uguryildirim24/elicio/tests/test_cad.py

from __future__ import annotations

import importlib.util
import hashlib
import json
import math
import shutil
import subprocess
import sys
import tempfile
import unittest
from pathlib import Path

ROOT = Path(__file__).resolve().parents[1]
SCRIPT = ROOT / "scripts" / "cad" / "bte_fit_shell.py"
MANIFEST_SCRIPT = ROOT / "scripts" / "cad" / "manifest.py"
RENDER_SCRIPT = ROOT / "scripts" / "cad" / "render.py"
MANIFEST = ROOT / "docs" / "fab" / "cad" / "v1" / "manifest.json"
ARTWORK = ("render_medial.png", "render_lateral.png", "drawing.pdf")


def load_cad():
    spec = importlib.util.spec_from_file_location("bte_fit_shell", SCRIPT)
    module = importlib.util.module_from_spec(spec)
    assert spec.loader is not None
    sys.modules["bte_fit_shell"] = module
    spec.loader.exec_module(module)
    return module


CAD = load_cad()

try:
    import matplotlib  # noqa: F401

    HAS_MATPLOTLIB = True
except ImportError:
    HAS_MATPLOTLIB = False
try:
    import trimesh  # noqa: F401

    HAS_TRIMESH = True
except ImportError:
    HAS_TRIMESH = False
HAS_RENDER = HAS_MATPLOTLIB and HAS_TRIMESH
# Review r7: a build needs the whole cad extra, not only build123d: STL checks
# use trimesh and the packing overlays import placement.py (matplotlib). With
# part of the extra missing the build tests skip by name instead of erroring.
HAS_CAD_BUILD = CAD.HAS_BUILD123D and HAS_RENDER
CAD_BUILD_SKIP = "needs the cad extra: build123d, trimesh and matplotlib"
PLACEMENT_SKIP = "needs matplotlib (cad or sheets extra): placement.py draws with it"


def load_manifest_mod():
    spec = importlib.util.spec_from_file_location("cad_manifest", MANIFEST_SCRIPT)
    module = importlib.util.module_from_spec(spec)
    assert spec.loader is not None
    spec.loader.exec_module(module)
    return module


def load_render_mod():
    spec = importlib.util.spec_from_file_location("cad_render", RENDER_SCRIPT)
    module = importlib.util.module_from_spec(spec)
    assert spec.loader is not None
    spec.loader.exec_module(module)
    return module


class CadMathTests(unittest.TestCase):
    def test_default_chord_and_radius_match_plan(self) -> None:
        path = CAD.make_path(48.4, 3.0)
        self.assertAlmostEqual(path.chord, 47.9005234, places=6)
        self.assertAlmostEqual(path.radius, 97.1025059, places=6)

    def test_origin_and_mid_arc_and_tail(self) -> None:
        path = CAD.make_path(48.4, 3.0)
        self.assertEqual(CAD.p_xyz(path, 0.0, 0.0, 0.0), (0.0, 0.0, 0.0))
        mid = CAD.p_xyz(path, 0.0, 24.2, 0.0)
        self.assertAlmostEqual(mid[0], 3.0, places=6)
        tail = CAD.p_xyz(path, 0.0, 48.4, 0.0)
        self.assertAlmostEqual(tail[0], 0.0, places=6)
        self.assertAlmostEqual(tail[2], -path.chord, places=6)

    def test_chord_gate_at_bow_1_and_3(self) -> None:
        gate3 = CAD.make_path(48.4, 3.0).chord + 3.0
        gate1 = CAD.make_path(48.4, 1.0).chord + 3.0
        self.assertAlmostEqual(gate3, 50.9005234, places=6)
        self.assertAlmostEqual(gate1, 51.3448596, places=6)

    def test_wire_channel_openings_match_finding_23(self) -> None:
        expected = {
            1.0: (39.4444, 1.0891),
            3.0: (39.6437, 0.9383),
            8.0: (40.0750, 0.5373),
        }
        for bow, (s_entry, physical) in expected.items():
            with self.subTest(bow=bow):
                report = CAD.wire_channel_opening(CAD.make_path(48.4, bow).radius)
                self.assertAlmostEqual(report["s_entry"], s_entry, places=3)
                self.assertAlmostEqual(report["physical_opening"], physical, places=3)
                self.assertGreater(report["physical_opening"], 0.0)

    def test_crease_bow_clamp(self) -> None:
        self.assertEqual(CAD.clamp_crease_bow(0.2), 1.0)
        self.assertEqual(CAD.clamp_crease_bow(11.0), 8.0)
        self.assertEqual(CAD.clamp_crease_bow(3.0), 3.0)


class CadCheckTests(unittest.TestCase):
    def test_m1_below_gate_fails_with_parameter_and_number(self) -> None:
        with self.assertRaises(CAD.CheckFail) as ctx:
            CAD.cli(["--set", "M1=40", "--checks-only"])
        message = str(ctx.exception)
        self.assertIn("M1", message)
        self.assertIn("40", message)
        self.assertIn("gate", message)

    def test_variant_outside_matrix_fails_before_export(self) -> None:
        with self.assertRaises(CAD.CheckFail) as ctx:
            CAD.cli(["--set", "VARIANT=medium", "--checks-only"])
        message = str(ctx.exception)
        self.assertIn("VARIANT", message)
        self.assertIn("medium", message)

    def test_preload_outside_matrix_fails_before_export(self) -> None:
        with self.assertRaises(CAD.CheckFail) as ctx:
            CAD.cli(["--set", "HOOK_PRELOAD=3", "--checks-only"])
        message = str(ctx.exception)
        self.assertIn("HOOK_PRELOAD", message)
        self.assertIn("3", message)

    def test_reference_checks_pass(self) -> None:
        self.assertEqual(CAD.cli(["--checks-only"]), 0)

    def test_plan_named_checks_are_present(self) -> None:
        params, _used = CAD.build_reference_params(variant="full", preload=1.5)
        names = {check.name for check in CAD.run_pre_cad_checks(params)}
        for expected in (
            "matrix",
            "M1_gate",
            "HOOK_RADIUS",
            "CONTACT_STACK",
            "keep-out: CONTACT_1 to superior low-u pad",
            "fit: tongue 0.5 : slot 0.9, y",
            "wall: top end wall at LIP_GROOVE",
            "E1",
            "E5_bump",
            "WIRE_CHANNEL_opening",
        ):
            self.assertIn(expected, names)

    def test_pad_keepout_gap_is_positive_at_supported_bows(self) -> None:
        for bow in (1.0, 3.0, 8.0):
            with self.subTest(bow=bow):
                params, _used = CAD.build_reference_params(
                    variant="full", preload=1.5, overrides={"CREASE_BOW": bow}
                )
                path = CAD.make_path(48.4, bow)
                gaps = CAD.keepout_clearances(params, path)
                self.assertGreater(gaps["CONTACT_1 to superior low-u pad"], 0.09)

    def test_fit_drift_fails(self) -> None:
        params, _used = CAD.build_reference_params(variant="full", preload=1.5)
        original = CAD.LIP_S
        CAD.LIP_S = (-1.2, -0.1)
        try:
            with self.assertRaises(CAD.CheckFail) as ctx:
                CAD.run_pre_cad_checks(params)
        finally:
            CAD.LIP_S = original
        self.assertIn("E5_lip", str(ctx.exception))


class CadOverlayTests(unittest.TestCase):
    def _params(self, argv: list[str]) -> dict:
        args = CAD.parse_args(argv)
        overrides, from_m = CAD.resolve_overrides(args)
        params, _used = CAD.build_reference_params(
            variant="full", preload=1.5, overrides=overrides, crease_bow_from_m=from_m
        )
        return params

    def _overlay(self, text: str) -> Path:
        handle = tempfile.NamedTemporaryFile("w", suffix=".toml", delete=False)
        handle.write(text)
        handle.close()
        self.addCleanup(Path(handle.name).unlink)
        return Path(handle.name)

    def test_default_toml_as_params_is_not_an_overlay(self) -> None:
        args = CAD.parse_args(["--params", str(CAD.DEFAULT_PARAMS_PATH)])
        overrides, from_m = CAD.resolve_overrides(args)
        self.assertEqual(overrides, {})
        self.assertFalse(from_m)

    def test_empty_overlay_keeps_default_bow(self) -> None:
        params = self._params(["--params", str(self._overlay("# nothing measured\n"))])
        self.assertEqual(params["CREASE_BOW"], 3.0)

    def test_overlay_with_m1_only_keeps_default_bow(self) -> None:
        params = self._params(["--params", str(self._overlay("M1 = 53.0\n"))])
        self.assertEqual(params["CREASE_BOW"], 3.0)

    def test_overlay_with_m1_and_m2_computes_and_clamps_bow(self) -> None:
        params = self._params(["--params", str(self._overlay("M1 = 52.0\nM2 = 58.0\n"))])
        self.assertAlmostEqual(params["CREASE_BOW_COMPUTED"], 11.0014, places=3)
        self.assertEqual(params["CREASE_BOW"], 8.0)

    def test_overlay_crease_bow_wins_over_m1_m2(self) -> None:
        text = "M1 = 52.0\nM2 = 58.0\nCREASE_BOW = 2.0\n"
        params = self._params(["--params", str(self._overlay(text))])
        self.assertEqual(params["CREASE_BOW"], 2.0)

    def test_m8_drives_hook_radius(self) -> None:
        params = self._params(["--set", "M8=13"])
        self.assertAlmostEqual(params["HOOK_RADIUS"], 13.0 + 1.75 + 0.75)
        self.assertEqual(CAD.cli(["--set", "M8=13", "--checks-only"]), 0)

    def test_unknown_key_fails(self) -> None:
        with self.assertRaises(CAD.CheckFail) as ctx:
            CAD.cli(["--set", "M9=12", "--checks-only"])
        self.assertIn("M9", str(ctx.exception))

    def test_fixed_geometry_key_fails(self) -> None:
        with self.assertRaises(CAD.CheckFail) as ctx:
            CAD.cli(["--set", "BODY_WIDTH=15", "--checks-only"])
        self.assertIn("BODY_WIDTH=15", str(ctx.exception))

    @unittest.skipUnless(HAS_MATPLOTLIB, PLACEMENT_SKIP)
    def test_stage_b_mock_false_checks_run(self) -> None:
        self.assertEqual(
            CAD.cli(["--set", "MOCK_CONTACTS=false", "--set", "CABLE_EXIT_S=35", "--checks-only"]), 0
        )
        params, _used = CAD.build_reference_params(
            variant="full", preload=1.5, overrides={"MOCK_CONTACTS": False, "CABLE_EXIT_S": 35.0}
        )
        names = {check.name: check for check in CAD.run_pre_cad_checks(params)}
        self.assertFalse(names["Q21_REF_lug pre-CAD"].passed)
        self.assertNotIn("E1", names)
        self.assertNotIn("E5_bump", names)
        for name in (
            "PLACEMENT_contacts",
            "BOARD_underside_clear pre-CAD",
            "CELL_envelope pre-CAD",
            "CABLE_EXIT_cavity pre-CAD",
            "TAB_envelope_air pre-CAD",
            "M1_gate",
        ):
            self.assertTrue(names[name].passed, name)


@unittest.skipUnless(HAS_CAD_BUILD, CAD_BUILD_SKIP)
class CadRegenTests(unittest.TestCase):
    def test_reference_regen_matches_committed_hashes(self) -> None:
        manifest = json.loads(MANIFEST.read_text(encoding="utf-8"))
        expected = {
            f"{part}.{ext}" for part in CAD.ORDER_PARTS for ext in ("step", "stl", "3mf")
        }
        self.assertEqual(set(manifest["files"]), expected)
        self.assertEqual(manifest["parts"], list(CAD.ORDER_PARTS))
        self.assertEqual(sum(manifest["quantities"].values()), 6)
        committed = {p.name for p in MANIFEST.parent.iterdir()}
        # placement*.svg are WP6 drawings, regenerated by tests/test_placement.py.
        placement = {
            "placement.svg",
            "placement_A.svg",
            "placement_B.svg",
            "placement_C.svg",
            "placement_E.svg",
        }
        v2_drawings = {p.name for p in MANIFEST.parent.glob("placement_v2_*.svg")}
        self.assertGreaterEqual(len(v2_drawings), 1)
        self.assertEqual(committed, expected | {"manifest.json"} | placement | set(ARTWORK) | v2_drawings)
        for name, meta in manifest["files"].items():
            with self.subTest(committed=name):
                self.assertEqual(
                    CAD.sha256_file(MANIFEST.parent / name), meta["sha256"], name
                )
        with tempfile.TemporaryDirectory() as temp_dir:
            CAD.build_and_export(Path(temp_dir))
            written = {p.name for p in Path(temp_dir).iterdir()}
            self.assertEqual(written, expected | {"manifest.json"})
            regenerated = json.loads((Path(temp_dir) / "manifest.json").read_text("utf-8"))
            for name in sorted(expected):
                with self.subTest(regenerated=name):
                    path = Path(temp_dir) / name
                    self.assertEqual(CAD.sha256_file(path), manifest["files"][name]["sha256"])
                    self.assertEqual(
                        regenerated["files"][name]["sha256"], manifest["files"][name]["sha256"]
                    )
            self.assertTrue(all(check["passed"] for check in regenerated["checks"]))
            self.assertEqual(regenerated["commit"], manifest["commit"])
            self.assertNotIn("views", regenerated)
            # Everything else the writer records must match the committed file,
            # so a generator change (a new note, a changed check) cannot leave
            # a stale manifest behind.
            committed_rest = {
                k: v for k, v in manifest.items() if not k.startswith("views")
            }
            self.assertEqual(regenerated, committed_rest)


class ManifestSchemaTests(unittest.TestCase):
    def test_committed_manifest_validates(self) -> None:
        mod = load_manifest_mod()
        payload = mod.load_manifest(MANIFEST)
        mod.validate(payload)
        mod.validate_bytes(payload, MANIFEST.parent)

    def test_validator_rejects_missing_key(self) -> None:
        mod = load_manifest_mod()
        payload = json.loads(MANIFEST.read_text(encoding="utf-8"))
        del payload["files"]
        with self.assertRaises(mod.ManifestError) as ctx:
            mod.validate(payload)
        self.assertIn("files", str(ctx.exception))
        self.assertIn("missing key", str(ctx.exception))


@unittest.skipUnless(HAS_RENDER, "needs the cad extra: matplotlib/trimesh is not installed")
class CadRenderTests(unittest.TestCase):
    def test_renders_and_drawing_regen_byte_identical(self) -> None:
        render = load_render_mod()
        v1 = MANIFEST.parent
        with tempfile.TemporaryDirectory() as temp_dir:
            dest = Path(temp_dir)
            for name in ("body_full_p15.stl", "body_thin_p15.stl", "lid.stl", "manifest.json"):
                shutil.copy2(v1 / name, dest / name)
            self.assertEqual(render.main(["--out", str(dest)]), 0)
            for name in ARTWORK:
                with self.subTest(name=name):
                    self.assertEqual(
                        CAD.sha256_file(dest / name),
                        CAD.sha256_file(v1 / name),
                        name,
                    )
            again = Path(tempfile.mkdtemp())
            self.addCleanup(shutil.rmtree, again, True)
            for name in ("body_full_p15.stl", "body_thin_p15.stl", "lid.stl", "manifest.json"):
                shutil.copy2(v1 / name, again / name)
            self.assertEqual(render.main(["--out", str(again)]), 0)
            committed_views = json.loads(MANIFEST.read_text(encoding="utf-8"))["views"]
            rendered_views = json.loads((again / "manifest.json").read_text("utf-8"))["views"]
            self.assertEqual(rendered_views, committed_views)
            for name in ARTWORK:
                with self.subTest(second=name):
                    self.assertEqual(
                        CAD.sha256_file(dest / name),
                        CAD.sha256_file(again / name),
                        name,
                    )


@unittest.skipUnless(HAS_CAD_BUILD, CAD_BUILD_SKIP)
class CadBuildGuardTests(unittest.TestCase):
    def test_clamp_limits_build_one_solid(self) -> None:
        for bow in (1.0, 8.0):
            with self.subTest(bow=bow), tempfile.TemporaryDirectory() as temp_dir:
                result = CAD.build_and_export(
                    Path(temp_dir), overrides={"CREASE_BOW": bow}, parts=("body_full_p15",)
                )
                self.assertEqual(len(result["files"]), 3)

    def test_subset_build_refuses_to_leave_stale_parts(self) -> None:
        with tempfile.TemporaryDirectory() as temp_dir:
            (Path(temp_dir) / "manifest.json").write_text(
                json.dumps({"files": {"body_thin_p15.stl": {}}}), encoding="utf-8"
            )
            with self.assertRaises(CAD.CheckFail) as ctx:
                CAD.build_and_export(Path(temp_dir), parts=("coupon",))
            self.assertIn("body_thin_p15", str(ctx.exception))

    def test_m1_below_gate_does_not_write_files(self) -> None:
        with tempfile.TemporaryDirectory() as temp_dir:
            with self.assertRaises(CAD.CheckFail):
                CAD.cli(
                    [
                        "--set",
                        "M1=40",
                        "--out",
                        temp_dir,
                    ]
                )
            self.assertEqual(list(Path(temp_dir).iterdir()), [])


STAGE_B_FILE = ROOT / "scripts" / "cad" / "params" / "stageb_provisional.toml"
# The provisional reading: plan §3.3 CABLE_EXIT s 36 cuts a corner pad (review r4 decision 24).
STAGE_B_BASE = {"MOCK_CONTACTS": False, "CABLE_EXIT_S": 35.0}


def stage_b_params(overrides: dict | None = None, variant: str = "full") -> dict:
    merged = dict(STAGE_B_BASE)
    merged.update(overrides or {})
    params, _used = CAD.build_reference_params(variant=variant, preload=1.5, overrides=merged)
    return params


@unittest.skipUnless(HAS_MATPLOTLIB, PLACEMENT_SKIP)
class CadStageBTests(unittest.TestCase):
    def test_packing_a_is_plan_shell(self) -> None:
        params = stage_b_params({"PACKING": "A"})
        self.assertEqual(params["PACKING"], "A")
        self.assertAlmostEqual(params["BODY_WIDTH"], 17.0)
        self.assertAlmostEqual(params["BODY_ARC"], 48.4)

    def test_packing_c_widens_body_and_uses_placement_pads(self) -> None:
        params = stage_b_params({"PACKING": "C"})
        self.assertEqual(params["PACKING"], "C")
        self.assertAlmostEqual(params["BODY_WIDTH"], 20.0)
        self.assertEqual(params["CAVITY_U"], [1.5, 18.5])
        self.assertEqual(params["LEAD_PADS"]["SIG1"], [7.5, 29.35])
        self.assertEqual(params["LEAD_PADS"]["SIG2"], [13.5, 21.35])
        self.assertEqual(params["LEAD_PADS"]["REF"], [5.5, 29.35])
        placement = CAD.load_placement()
        self.assertEqual(
            params["LEAD_PADS"]["SIG1"],
            list(placement.PADS_BY_OPTION["C"]["SIG1"]),
        )

    def test_packing_b_lengthens_arc_and_moves_tail(self) -> None:
        params = stage_b_params({"PACKING": "B"})
        self.assertAlmostEqual(params["BODY_ARC"], 51.9)
        self.assertAlmostEqual(params["TAIL_DS"], 3.5)
        self.assertAlmostEqual(params["TAIL_S0"], 41.7)
        self.assertAlmostEqual(params["CONTACT_REF_S"], 46.5)
        self.assertEqual(params["WIRE_S"], [41.7, 44.0])

    def test_pads_are_not_copied_into_the_cad_script(self) -> None:
        text = SCRIPT.read_text(encoding="utf-8")
        self.assertNotIn("29.35", text)
        self.assertNotIn("21.35", text)

    def test_q21_pre_cad_records_failure_with_numbers(self) -> None:
        params = stage_b_params()
        q21 = {c.name: c for c in CAD.run_pre_cad_checks(params)}["Q21_REF_lug pre-CAD"]
        self.assertFalse(q21.passed)
        self.assertEqual(q21.numbers["lug_top_y"], 8.23)
        self.assertEqual(q21.numbers["lid_y"], 8.0)
        self.assertEqual(q21.numbers["barrel_outer"], 4.54)
        self.assertEqual(q21.numbers["pocket_r"], 3.75)

    def test_keepout_on_rib_fails_with_gap(self) -> None:
        with self.assertRaises(CAD.CheckFail) as ctx:
            CAD.cli(
                ["--set", "MOCK_CONTACTS=false", "--set", "CONTACT_1_S=17.9", "--checks-only"]
            )
        message = str(ctx.exception)
        self.assertIn("keep-out", message)
        self.assertIn("gap", message)

    def test_tab_height_3_fails_board_clearance(self) -> None:
        with self.assertRaises(CAD.CheckFail) as ctx:
            CAD.cli(["--set", "MOCK_CONTACTS=false", "--set", "TAB_HEIGHT=3", "--checks-only"])
        message = str(ctx.exception)
        self.assertIn("BOARD_underside_clear", message)
        self.assertIn("envelope_top=4.5", message)

    def test_cable_exit_in_battery_fails(self) -> None:
        with self.assertRaises(CAD.CheckFail) as ctx:
            CAD.cli(
                ["--set", "MOCK_CONTACTS=false", "--set", "CABLE_EXIT_S=10", "--checks-only"]
            )
        message = str(ctx.exception)
        self.assertIn("CABLE_EXIT_cavity", message)
        self.assertIn("CABLE_EXIT_S=10", message)
        self.assertIn("board_side_of_rib=0.0", message)

    def test_cable_exit_at_plan_s36_meets_a_corner_pad_pre_cad(self) -> None:
        with self.assertRaises(CAD.CheckFail) as ctx:
            CAD.cli(["--set", "MOCK_CONTACTS=false", "--checks-only"])
        self.assertIn("CABLE_EXIT_cavity pre-CAD", str(ctx.exception))
        self.assertIn("corner_pad_s_gap=-0.6", str(ctx.exception))

    def test_cell_too_wide_fails(self) -> None:
        params = stage_b_params()
        original = CAD.BATTERY_U
        CAD.BATTERY_U = (3.1, 8.0)
        try:
            with self.assertRaises(CAD.CheckFail) as ctx:
                CAD.run_pre_cad_checks(params)
        finally:
            CAD.BATTERY_U = original
        self.assertIn("CELL_envelope", str(ctx.exception))
        self.assertIn("clear_u=-5.5", str(ctx.exception))

    def test_cell_does_not_fit_a_thin_body_pre_cad(self) -> None:
        with self.assertRaises(CAD.CheckFail) as ctx:
            CAD.run_pre_cad_checks(stage_b_params(variant="thin"))
        self.assertIn("CELL_envelope pre-CAD", str(ctx.exception))
        self.assertIn("clear_y=-1.2", str(ctx.exception))

    def test_closure_passed_restores_e1_e3_e5(self) -> None:
        names = {c.name for c in CAD.run_pre_cad_checks(stage_b_params({"CLOSURE_PASSED": True}))}
        self.assertIn("E1", names)
        self.assertIn("E3", names)
        self.assertIn("E5_bump", names)
        names = {c.name for c in CAD.run_pre_cad_checks(stage_b_params())}
        self.assertNotIn("E1", names)

    def test_provisional_file_defaults(self) -> None:
        args = CAD.parse_args(["--params", str(STAGE_B_FILE)])
        overrides, _from_m = CAD.resolve_overrides(args)
        self.assertFalse(overrides["MOCK_CONTACTS"])
        self.assertEqual(overrides["PACKING"], "C")
        self.assertFalse(overrides["CLOSURE_PASSED"])
        self.assertEqual(overrides["TAB_HEIGHT"], 2.0)
        self.assertEqual(overrides["CABLE_EXIT_S"], 35.0)
        header = STAGE_B_FILE.read_text(encoding="utf-8")
        for question in ("Q20", "Q22", "Q21", "Q18", "Q11", "Q17", "WP7a", "decision 24", "decision 25"):
            self.assertIn(question, header)

    def test_order1_overlay_refuses_stage_b_keys(self) -> None:
        for item in ("CONTACT_1_U=7.0", "PACKING=B", "CLOSURE_PASSED=true", "CABLE_EXIT_S=35"):
            with self.subTest(item=item):
                with self.assertRaises(CAD.CheckFail) as ctx:
                    CAD.cli(["--set", item, "--checks-only"])
                self.assertIn("MOCK_CONTACTS = false", str(ctx.exception))
                self.assertIn(item.split("=")[0], str(ctx.exception))

    def test_stage_b_contacts_off_the_placement_sites_fail(self) -> None:
        with self.assertRaises(CAD.CheckFail) as ctx:
            CAD.run_pre_cad_checks(stage_b_params({"CONTACT_1_S": 22.5}))
        message = str(ctx.exception)
        self.assertIn("PLACEMENT_contacts", message)
        self.assertIn("drift=0.5", message)

    def test_stage_b_refuses_v1_out(self) -> None:
        params = stage_b_params()
        with self.assertRaises(CAD.CheckFail) as ctx:
            CAD.assert_stage_b_out_dir(CAD.V1_DIR, params)
        self.assertIn("v1", str(ctx.exception).lower())
        with self.assertRaises(CAD.CheckFail):
            CAD.assert_stage_b_out_dir(CAD.V2_DIR, params)

    def test_stage_b_manifest_validator(self) -> None:
        mod = load_manifest_mod()
        payload = json.loads(MANIFEST.read_text(encoding="utf-8"))
        mod.validate(payload)
        row = {"passed": True, "detail": "d", "numbers": {}, "bodies": {"body_full_p15": {"passed": True}}}
        payload.update(
            stage="B",
            provisional=True,
            packing="C",
            closure_passed=False,
            contact_source="plan §3.3 defaults",
            stage_b={name: dict(row) for name in mod.STAGE_B_CHECKS},
            stage_b_failing=[],
            stage_b_passed=True,
        )
        mod.validate(payload)
        payload["stage_b"]["Q21_REF_lug"] = {**row, "passed": False, "bodies": {"body_full_p15": {"passed": False}}}
        with self.assertRaises(mod.ManifestError):
            mod.validate(payload)
        payload["stage_b_failing"] = ["Q21_REF_lug"]
        with self.assertRaises(mod.ManifestError):
            mod.validate(payload)
        payload["stage_b_passed"] = False
        mod.validate(payload)
        del payload["stage_b"]["CELL_envelope"]
        with self.assertRaises(mod.ManifestError):
            mod.validate(payload)


@unittest.skipUnless(HAS_CAD_BUILD, CAD_BUILD_SKIP)
class CadStageBBuildTests(unittest.TestCase):
    """Stage B checks measured on solids: one passing body, then each check's
    failing case with the parameter that breaks it and the number it reports."""

    @classmethod
    def setUpClass(cls) -> None:
        cls.params = stage_b_params()
        cls.body, cls.lid, cls.path, cls.notes = CAD.build_body_and_lid(cls.params)

    def rows(self, params=None, body=None, lid=None, notes=None) -> dict:
        checks = CAD.run_stage_b_solid_checks(
            body or self.body,
            lid or self.lid,
            self.path,
            params or self.params,
            (notes or self.notes)["stage_b_cuts"],
            raise_on_fail=False,
        )
        return {c.name: c for c in checks}

    def test_provisional_c_passes_every_check_but_q21(self) -> None:
        rows = self.rows()
        self.assertEqual(set(rows), set(CAD.STAGE_B_CHECK_NAMES))
        self.assertEqual([n for n, c in rows.items() if not c.passed], ["Q21_REF_lug"])
        q21 = rows["Q21_REF_lug"].numbers
        self.assertEqual(q21["lug_top_y"], 8.23)
        self.assertEqual(q21["lid_y"], 8.0)
        self.assertEqual(q21["barrel_outer"], 4.54)
        self.assertEqual(q21["pocket_r"], 3.75)
        self.assertEqual(rows["CONTACT_HOLE_wall"].numbers["removed_SIG1_mm3"], 9.9078)
        self.assertEqual(rows["BOARD_underside_clear"].numbers["board_underside"], 4.3)
        self.assertEqual(rows["CELL_envelope"].numbers["clear_y_lid"], 0.4)
        # Q21 is recorded, not raised.
        CAD.run_stage_b_solid_checks(self.body, self.lid, self.path, self.params, self.notes["stage_b_cuts"])

    def test_stage_b_lid_is_not_embossed_as_the_order1_gauge(self) -> None:
        self.assertEqual(self.notes["emboss"], "ELICIO V2 R FULL P15 REF")
        self.assertEqual(self.notes["emboss_h"], 0.4)
        self.assertEqual(self.notes["emboss_s"], 10.0)

    def test_keepout_signal_fails_when_nylon_is_inside(self) -> None:
        params = dict(self.params, CONTACT_1_S=19.0)
        row = self.rows(params)["KEEPOUT_SIGNAL_air"]
        self.assertFalse(row.passed)
        self.assertGreater(row.numbers["SIG1_body_mm3"], 1.0)
        with self.assertRaises(CAD.CheckFail) as ctx:
            CAD.run_stage_b_solid_checks(self.body, self.lid, self.path, params, self.notes["stage_b_cuts"])
        self.assertIn("KEEPOUT_SIGNAL_air", str(ctx.exception))

    def test_tab_envelope_fails_into_the_side_wall(self) -> None:
        params = dict(self.params, TAB_DEG={"SIG1": 110.0, "SIG2": 0.0})
        row = self.rows(params)["TAB_envelope_air"]
        self.assertFalse(row.passed)
        self.assertGreater(row.numbers["SIG2_body_mm3"], 0.5)
        self.assertEqual(row.numbers["SIG1_body_mm3"], 0.0)

    def test_board_underside_fails_with_a_3_mm_tab(self) -> None:
        row = self.rows(dict(self.params, TAB_HEIGHT=3.0))["BOARD_underside_clear"]
        self.assertFalse(row.passed)
        self.assertEqual(row.numbers["envelope_top"], 4.5)
        self.assertEqual(row.numbers["board_underside"], 4.3)

    def test_ref_wire_fails_when_it_runs_in_the_floor(self) -> None:
        original = CAD.WIRE_Y
        CAD.WIRE_Y = (0.4, 2.0)
        try:
            row = self.rows()["REF_WIRE_envelope"]
        finally:
            CAD.WIRE_Y = original
        self.assertFalse(row.passed)
        self.assertGreater(row.numbers["body_mm3"], 1.0)

    def test_closure_flag_must_match_the_solids(self) -> None:
        row = self.rows(dict(self.params, CLOSURE_PASSED=True))["CLOSURE_PASSED"]
        self.assertFalse(row.passed)
        self.assertEqual(row.numbers["flag"], 1.0)
        self.assertEqual(row.numbers["tongue"], 0.0)

    def test_hole_in_side_wall_fails_wall_only_check(self) -> None:
        params = stage_b_params({"CONTACT_1_U": 0.5})
        body, lid, path, notes = CAD.build_body_and_lid(params)
        with self.assertRaises(CAD.CheckFail) as ctx:
            CAD.run_stage_b_solid_checks(body, lid, path, params, notes["stage_b_cuts"])
        self.assertIn("CONTACT_HOLE_wall", str(ctx.exception))
        removed = notes["stage_b_cuts"]["hole_removed_mm3"]["SIG1"]
        self.assertLess(removed, 0.98 * 9.9078)

    def test_cable_exit_at_plan_s36_cuts_a_corner_pad(self) -> None:
        params = stage_b_params({"CABLE_EXIT_S": 36.0})
        body, lid, path, notes = CAD.build_body_and_lid(params)
        row = self.rows(params, body, lid, notes)["CABLE_EXIT_cavity"]
        self.assertFalse(row.passed)
        self.assertAlmostEqual(row.numbers["nylon_in_cavity_mm3"], 0.99, delta=0.01)

    def test_cell_envelope_fails_on_a_thin_body(self) -> None:
        params = stage_b_params(variant="thin")
        body, lid, path, notes = CAD.build_body_and_lid(params)
        rows = {
            c.name: c
            for c in CAD.run_stage_b_solid_checks(
                body, lid, path, params, notes["stage_b_cuts"], raise_on_fail=False
            )
        }
        row = rows["CELL_envelope"]
        self.assertFalse(row.passed)
        self.assertGreater(row.numbers["lid_mm3"], 150.0)
        self.assertEqual(rows["Q21_REF_lug"].numbers["lid_y"], 6.0)

    def test_closure_passed_puts_the_e1_web_in_the_ref_pocket(self) -> None:
        params = stage_b_params({"CLOSURE_PASSED": True})
        body, lid, path, notes = CAD.build_body_and_lid(params)
        rows = {
            c.name: c
            for c in CAD.run_stage_b_solid_checks(
                body, lid, path, params, notes["stage_b_cuts"], raise_on_fail=False
            )
        }
        self.assertTrue(rows["CLOSURE_PASSED"].passed)
        ref = rows["KEEPOUT_REF_air"]
        self.assertFalse(ref.passed)
        self.assertAlmostEqual(ref.numbers["pocket_lid_mm3"], 2.48, delta=0.02)

    def test_guard_refuses_a_build_without_every_stage_b_check(self) -> None:
        original = CAD.run_stage_b_solid_checks

        def partial(*args, **kwargs):
            return [c for c in original(*args, **kwargs) if c.name != "CELL_envelope"]

        CAD.run_stage_b_solid_checks = partial
        try:
            with tempfile.TemporaryDirectory() as temp_dir:
                with self.assertRaises(CAD.CheckFail) as ctx:
                    CAD.build_and_export(
                        Path(temp_dir), overrides=dict(STAGE_B_BASE), parts=("body_full_p15",)
                    )
                self.assertEqual(list(Path(temp_dir).iterdir()), [])
        finally:
            CAD.run_stage_b_solid_checks = original
        self.assertIn("Stage B checks missing", str(ctx.exception))
        self.assertIn("CELL_envelope", str(ctx.exception))

    def test_stage_b_build_needs_a_body(self) -> None:
        with tempfile.TemporaryDirectory() as temp_dir:
            with self.assertRaises(CAD.CheckFail) as ctx:
                CAD.build_and_export(Path(temp_dir), overrides=dict(STAGE_B_BASE), parts=("lid",))
        self.assertIn("needs a body", str(ctx.exception))

    def test_provisional_build_from_the_readme_command(self) -> None:
        cmd = [sys.executable, str(SCRIPT), "--params", str(STAGE_B_FILE)]
        payloads = []
        for _ in range(2):
            with tempfile.TemporaryDirectory() as temp_dir:
                dest = Path(temp_dir)
                done = subprocess.run(cmd + ["--out", str(dest)], capture_output=True, text=True)
                self.assertEqual(done.returncode, CAD.STAGE_B_NOT_PASSED_EXIT, done.stderr)
                self.assertIn("STAGE B NOT PASSED", done.stderr)
                self.assertIn("Q21_REF_lug", done.stderr)
                payload = json.loads((dest / "manifest.json").read_text(encoding="utf-8"))
                self.assertEqual(
                    sorted(p.name for p in dest.iterdir()),
                    sorted(
                        [f"{part}.{ext}" for part in CAD.STAGE_B_PARTS for ext in ("3mf", "step", "stl")]
                        + ["manifest.json"]
                    ),
                )
                payloads.append(payload)
        payload, again = payloads
        self.assertEqual(again["files"], payload["files"])
        self.assertEqual(payload["stage"], "B")
        self.assertTrue(payload["provisional"])
        self.assertEqual(payload["packing"], "C")
        self.assertFalse(payload["closure_passed"])
        self.assertIn("plan §3.3", payload["contact_source"])
        self.assertFalse(payload["stage_b_passed"])
        self.assertEqual(payload["stage_b_failing"], ["Q21_REF_lug"])
        self.assertEqual(sorted(payload["stage_b"]), sorted(CAD.STAGE_B_CHECK_NAMES))
        q21 = payload["stage_b"]["Q21_REF_lug"]
        self.assertEqual(sorted(q21["bodies"]), ["body_full_p15", "body_full_p25"])
        self.assertEqual(
            (q21["numbers"]["lug_top_y"], q21["numbers"]["lid_y"]), (8.23, 8.0)
        )
        self.assertEqual(
            (q21["numbers"]["barrel_outer"], q21["numbers"]["pocket_r"]), (4.54, 3.75)
        )
        for name, row in payload["stage_b"].items():
            if name != "Q21_REF_lug":
                self.assertTrue(row["passed"], name)
        self.assertNotIn("views", payload)
        load_manifest_mod().validate(payload)


@unittest.skipUnless(HAS_MATPLOTLIB, PLACEMENT_SKIP)
class CadStageBV2Tests(unittest.TestCase):
    def test_v2_packing_uses_width_20_and_lid_8(self) -> None:
        params = stage_b_params(
            {
                "PACKING": "v2",
                "V2_ARCH": "A",
                "V2_CELL": "501015",
                "V2_LAYOUT": "series",
                "V2_WIDTH": 20.0,
                "V2_LID_Y": 8.0,
                "V2_IFACE": "II",
                "V2_STANDOFF": 3.0,
            }
        )
        self.assertEqual(params["PACKING"], "v2")
        self.assertAlmostEqual(params["BODY_WIDTH"], 20.0)
        self.assertAlmostEqual(params["BODY_ARC"], 48.4)
        self.assertAlmostEqual(params["LID_Y"], 8.0)
        self.assertAlmostEqual(params["BODY_THICK"], 9.0)
        self.assertAlmostEqual(params["TOTAL_CHORD"], 47.9005, places=3)

    def test_v2_pre_cad_records_not_measured_tab_gap(self) -> None:
        params = stage_b_params(
            {
                "PACKING": "v2",
                "V2_ARCH": "A",
                "V2_CELL": "501015",
                "V2_LAYOUT": "series",
                "V2_WIDTH": 20.0,
                "V2_LID_Y": 8.0,
                "V2_IFACE": "II",
                "V2_STANDOFF": 3.0,
            }
        )
        rows = {c.name: c for c in CAD.run_pre_cad_checks(params)}
        tab = rows["TAB_envelope_air pre-CAD"]
        self.assertFalse(tab.passed)
        self.assertTrue(tab.detail.startswith("NOT_MEASURED"))
        q21 = rows["Q21_REF_lug pre-CAD"]
        self.assertTrue(q21.passed)
        self.assertIn("brass standoff", q21.detail)
        # Review r5: ring 0.31 + standoff 3.0 on the floor, no DIN 439 nut.
        self.assertAlmostEqual(q21.numbers["stack_top_y"], 4.81)
        self.assertAlmostEqual(q21.numbers["tip_below_top"], 0.81)


STAGE_B_V2_FILE = ROOT / "scripts" / "cad" / "params" / "stageb_v2.toml"


@unittest.skipUnless(HAS_CAD_BUILD, CAD_BUILD_SKIP)
class CadStageBV2BuildTests(unittest.TestCase):
    """Winner layout measured on the order-1 construction path."""

    @classmethod
    def setUpClass(cls) -> None:
        cls.params = stage_b_params(
            {
                "PACKING": "v2",
                "V2_ARCH": "A",
                "V2_CELL": "501015",
                "V2_LAYOUT": "series",
                "V2_WIDTH": 20.0,
                "V2_LID_Y": 8.0,
                "V2_IFACE": "II",
                "V2_STANDOFF": 3.0,
            }
        )
        cls.body, cls.lid, cls.path, cls.notes = CAD.build_body_and_lid(cls.params)

    def test_v2_solid_checks_include_measured_envelopes(self) -> None:
        checks = CAD.run_stage_b_solid_checks(
            self.body,
            self.lid,
            self.path,
            self.params,
            self.notes["stage_b_cuts"],
            raise_on_fail=False,
        )
        rows = {c.name: c for c in checks}
        for name in (
            "V2_CELL_envelope",
            "V2_MODULE_envelope",
            "V2_BOARD_envelope",
            "V2_TAB_envelope",
            "V2_CONTACT_STACK",
            "V2_LID_band",
            "V2_WALL_minima",
            "V2_TOTAL_CHORD",
            "V2_M1_gate",
            "V2_STANDOFF",
            "V2_ADJUSTMENT",
            "V2_USB_medial",
            "V2_HARNESS",
            "V2_BOSS",
            "V2_CELL_CLEARANCE",
            "V2_STACK",
            "V2_RECESS",
        ):
            self.assertIn(name, rows)
            self.assertFalse(
                rows[name].detail.startswith("NOT_MEASURED") and rows[name].passed,
                name,
            )
        self.assertAlmostEqual(rows["V2_TOTAL_CHORD"].numbers["TOTAL_CHORD"], 47.9005, places=3)
        self.assertTrue(rows["V2_M1_gate"].passed)
        self.assertTrue(rows["Q21_REF_lug"].passed)
        self.assertIn("body_mm3", rows["V2_BOARD_envelope"].numbers)
        self.assertIn("body_mm3", rows["V2_CELL_envelope"].numbers)
        # packing-v2.md §6 prints STAGE_B_V2_MEASURED; it must be this build.
        v2 = CAD.load_placement()._v2()
        for name, (status, nums, _text) in v2.STAGE_B_V2_MEASURED.items():
            with self.subTest(check=name):
                row = rows[name]
                if status == "NOT_MEASURED":
                    self.assertTrue(row.detail.startswith("NOT_MEASURED"), row.detail)
                    self.assertFalse(row.passed)
                else:
                    self.assertEqual(row.passed, status == "pass", row.detail)
                for key, value in nums.items():
                    self.assertAlmostEqual(row.numbers[key], value, places=3, msg=key)

    def test_two_consecutive_v2_stage_b_runs_are_identical(self) -> None:
        cmd = [sys.executable, str(SCRIPT), "--params", str(STAGE_B_V2_FILE)]
        hashes = []
        for _ in range(2):
            with tempfile.TemporaryDirectory() as temp_dir:
                dest = Path(temp_dir)
                done = subprocess.run(cmd + ["--out", str(dest)], capture_output=True, text=True)
                self.assertIn(done.returncode, (0, CAD.STAGE_B_NOT_PASSED_EXIT), done.stderr)
                payload = json.loads((dest / "manifest.json").read_text(encoding="utf-8"))
                hashes.append(payload["files"])
                self.assertEqual(payload["packing"], "v2")
                load_manifest_mod().validate(payload)
        self.assertEqual(hashes[0], hashes[1])


SHELL_FILE = ROOT / "scripts" / "cad" / "params" / "shell_v2.toml"


@unittest.skipUnless(HAS_MATPLOTLIB, PLACEMENT_SKIP)
class CadShellV2Tests(unittest.TestCase):
    def test_q71_screw_engagement_constant(self) -> None:
        self.assertGreaterEqual(CAD.SHELL_SCREW_ENGAGE, 4.0)
        self.assertGreaterEqual(CAD.SHELL_SCREW_LEN, 8.0)
        self.assertGreaterEqual(CAD.SHELL_LID_BOSS_H, 3.0)
        self.assertGreaterEqual(CAD.SHELL_LID_ENGAGE, 3.0)
        self.assertGreaterEqual(CAD.SHELL_SCREW_BOSS_WALL, 1.4)
        self.assertGreaterEqual(CAD.SHELL_SCREW_BOSS_OD, 5.0)
        self.assertAlmostEqual(CAD.SHELL_PILOT, 2.10)
        self.assertAlmostEqual(CAD.SHELL_SCREW_PILOT, 2.10)
        self.assertGreaterEqual(CAD.SHELL_LID_RIM_T, 1.0)
        self.assertGreaterEqual(CAD.SHELL_LID_RIM_R, 1.0)

    def test_shell_overlay_sets_stage_and_winner_layout(self) -> None:
        args = CAD.parse_args(["--params", str(SHELL_FILE), "--stage", "shell"])
        overrides, _from_m = CAD.resolve_overrides(args)
        overrides["STAGE"] = "shell"
        overrides.setdefault("MOCK_CONTACTS", False)
        params, _used = CAD.build_reference_params(
            variant="full", preload=1.5, overrides=overrides
        )
        self.assertTrue(CAD.stage_is_shell(params))
        self.assertEqual(params["PACKING"], "v2")
        self.assertEqual(params["V2_IFACE"], "II")
        self.assertAlmostEqual(params["V2_STANDOFF"], 3.0)
        self.assertAlmostEqual(params["LID_Y"], 8.0)
        self.assertAlmostEqual(params["BODY_WIDTH"], 22.0)
        self.assertEqual(params["V2_CELL"], "pack501012")
        self.assertAlmostEqual(params["BODY_THICK"], 9.0)
        self.assertAlmostEqual(params["TOTAL_CHORD"], 47.9005, places=3)
        self.assertAlmostEqual(params["CAVITY_U"][0], 1.5)
        self.assertAlmostEqual(params["CAVITY_U"][1], 20.5)
        self.assertAlmostEqual(params["BOARD_ZONE_U"][0], 2.25)
        self.assertAlmostEqual(params["BOARD_ZONE_U"][1], 19.75)
        self.assertAlmostEqual(params["BOARD_ZONE_S"][0], 16.0)
        self.assertAlmostEqual(params["RIB_S"][0], 14.9, places=1)
        header = SHELL_FILE.read_text(encoding="utf-8")
        for token in ("Q59", "Q34", "Harwin R25-1000402", "3.0", "Q71", "Q76", "Q81", "Q82", "Q83", "Q89", "Q90", "Q93", "Q98"):
            self.assertIn(token, header)

    def test_s5c_reader_uses_the_table(self) -> None:
        s5c = CAD.load_s5c_no_receptacle()
        self.assertEqual(s5c.packing_sha, CAD.S5D_PACKING_SHA)
        self.assertEqual(s5c.holes, ((13.45, 17.70), (17.95, 17.70)))
        self.assertEqual(s5c.p1, (5.90, 22.00))
        self.assertEqual(s5c.p2, (10.40, 33.10))
        self.assertEqual(s5c.p3, (8.50, 43.00))
        self.assertEqual(s5c.p4, (14.70, 4.30))
        self.assertEqual(s5c.p5, (17.70, 11.72))
        self.assertAlmostEqual(s5c.p4_y, 1.50)
        self.assertAlmostEqual(s5c.p5_y, 1.50)
        self.assertAlmostEqual(s5c.sig1_strip, 10.71, places=2)
        self.assertAlmostEqual(s5c.sig2_strip, 21.81, places=2)
        self.assertEqual(s5c.island_u, (2.25, 19.75))
        self.assertEqual(s5c.island_s, (16.00, 37.60))
        self.assertEqual(s5c.rib_slot_u, (11.90, 20.50))
        self.assertEqual(s5c.rib_slot_s, (14.90, 15.70))
        self.assertAlmostEqual(s5c.rib_slot_h, 0.31)
        self.assertAlmostEqual(s5c.drop_s0, 16.00)
        self.assertEqual(s5c.drop_u, (11.90, 20.50))
        self.assertAlmostEqual(s5c.drop_r, 1.5)
        self.assertAlmostEqual(s5c.drop_h, 3.31)
        self.assertAlmostEqual(s5c.drop_flex, 0.31)
        self.assertTrue(any(row[0] == "P4" for row in s5c.courtyards))
        folded = CAD.load_s5d_folded()
        self.assertEqual(folded.p4, s5c.p4)
        self.assertEqual(folded.p5, s5c.p5)
        inactive = CAD.Check("V2_USB_end", False, "NOT_APPLICABLE: Q81: no receptacle at M1 52")
        self.assertEqual(
            CAD.stage_b_failing({"full": {"V2_USB_end": inactive}}, skip_not_measured=True),
            [],
        )

    def test_s5e_reader_uses_the_wall_table(self) -> None:
        s5e = CAD.load_s5e_shell()
        self.assertEqual(s5e.packing_sha, CAD.S5E_PACKING_SHA)
        self.assertEqual(s5e.holes, ((13.23, 17.70), (17.95, 17.70)))
        self.assertEqual(s5e.p1, (5.90, 22.00))
        self.assertEqual(s5e.p2, (10.40, 33.10))
        self.assertEqual(s5e.p3, (8.50, 43.00))
        self.assertEqual(s5e.p4, (20.50, 4.35))
        self.assertEqual(s5e.p5, (20.50, 12.35))
        self.assertAlmostEqual(s5e.p4_y, 4.35)
        self.assertAlmostEqual(s5e.p5_y, 4.35)
        self.assertEqual(s5e.head_axis, "+u")
        self.assertIn("posterior", s5e.wall_name)
        self.assertEqual(s5e.j2, (15.15, 11.35))
        self.assertAlmostEqual(s5e.j2_wu, 5.80, places=2)
        self.assertAlmostEqual(s5e.j2_ws, 6.56, places=2)
        self.assertAlmostEqual(s5e.sig1_strip, 10.71, places=2)
        self.assertAlmostEqual(s5e.sig2_strip, 21.81, places=2)
        self.assertEqual(s5e.cavity_u, (1.50, 20.50))
        h1_h2 = abs(s5e.holes[0][0] - s5e.holes[1][0]) - CAD.S5C_BOSS_KEEP
        self.assertAlmostEqual(h1_h2, 1.42, places=2)
        frozen = CAD.load_s5d_folded()
        self.assertEqual(frozen.p4, (14.70, 4.30))
        self.assertEqual(frozen.holes, ((13.45, 17.70), (17.95, 17.70)))

    def test_shell_refuses_v1_and_allows_v2(self) -> None:
        params = stage_b_params(
            {
                "PACKING": "v2",
                "STAGE": "shell",
                "V2_ARCH": "A",
                "V2_CELL": "pack501012",
                "V2_LAYOUT": "series",
                "V2_WIDTH": 22.0,
                "V2_LID_Y": 8.0,
                "V2_IFACE": "II",
                "V2_STANDOFF": 3.0,
            }
        )
        with self.assertRaises(CAD.CheckFail) as ctx:
            CAD.assert_stage_b_out_dir(CAD.V1_DIR, params)
        self.assertIn("v1", str(ctx.exception).lower())
        CAD.assert_stage_b_out_dir(CAD.V2_DIR, params)


@unittest.skipUnless(HAS_CAD_BUILD, CAD_BUILD_SKIP)
class CadShellV2BuildTests(unittest.TestCase):
    """Wearable body on the §5d width-22 winner. Same construction path as Stage B v2."""

    @classmethod
    def setUpClass(cls) -> None:
        cls.params = stage_b_params(
            {
                "PACKING": "v2",
                "STAGE": "shell",
                "V2_ARCH": "A",
                "V2_CELL": "pack501012",
                "V2_LAYOUT": "series",
                "V2_WIDTH": 22.0,
                "V2_LID_Y": 8.0,
                "V2_IFACE": "II",
                "V2_STANDOFF": 3.0,
            }
        )
        cls.body, cls.lid, cls.path, cls.notes = CAD.build_body_and_lid(cls.params)

    def test_q59_and_new_checks_on_the_solid(self) -> None:
        checks = CAD.run_stage_b_solid_checks(
            self.body,
            self.lid,
            self.path,
            self.params,
            self.notes["stage_b_cuts"],
            raise_on_fail=False,
        )
        rows = {c.name: c for c in checks}
        self.assertTrue(rows["V2_TAB_envelope"].passed, rows["V2_TAB_envelope"].detail)
        self.assertTrue(rows["REF_WIRE_envelope"].passed, rows["REF_WIRE_envelope"].detail)
        self.assertLessEqual(rows["V2_TAB_envelope"].numbers["REF_body_mm3"], 0.005)
        self.assertLessEqual(rows["REF_WIRE_envelope"].numbers["body_mm3"], 0.005)
        for name in ("V2_BOSS", "V2_RING_seat", "V2_SWITCH_reach", "V2_STANDOFF"):
            self.assertIn(name, rows)
            self.assertTrue(rows[name].passed, f"{name}: {rows[name].detail} {rows[name].numbers}")
            self.assertFalse(rows[name].detail.startswith("NOT_MEASURED"), name)
        # Q89: lid boss into a tail pocket; M2.5×8 from the well; ≥ 3 mm of
        # thread in the lid boss; V2_CLOSURE passes.
        self.assertTrue(rows["V2_CLOSURE"].passed, rows["V2_CLOSURE"].numbers)
        self.assertAlmostEqual(rows["V2_CLOSURE"].numbers["screw_tip_y"], 9.55, places=2)
        self.assertLessEqual(rows["V2_CLOSURE"].numbers["lid_underside_y"], 5.05)
        self.assertGreaterEqual(rows["V2_CLOSURE"].numbers["lid_engagement"], 3.0)
        self.assertGreaterEqual(rows["V2_CLOSURE"].numbers["hinge_lip_undercut"], 1.0)
        self.assertGreaterEqual(rows["V2_CLOSURE"].numbers["boss_wall"], 1.4)
        self.assertEqual(rows["V2_CLOSURE"].numbers["well_on_medial"], 1.0)
        self.assertTrue(rows["V2_LATERAL_unbroken"].passed, rows["V2_LATERAL_unbroken"].numbers)
        self.assertEqual(rows["V2_LATERAL_unbroken"].numbers["pits"], 0.0)
        self.assertEqual(rows["V2_LATERAL_unbroken"].numbers["old_lid_well_solid"], 1.0)
        self.assertEqual(rows["V2_LATERAL_unbroken"].numbers["pad_closed"], 1.0)
        self.assertTrue(rows["V2_BOSS_pilot"].passed, rows["V2_BOSS_pilot"].numbers)
        self.assertAlmostEqual(rows["V2_BOSS_pilot"].numbers["tail_pilot_d"], 2.10, delta=0.08)
        self.assertGreaterEqual(rows["V2_BOSS_pilot"].numbers["tail_wall"], 1.4)
        self.assertGreaterEqual(rows["V2_BOSS_pilot"].numbers["tail_od"], 5.0)
        self.assertAlmostEqual(rows["V2_BOSS_pilot"].numbers["lid_pilot_d"], 2.10, delta=0.08)
        self.assertGreaterEqual(rows["V2_BOSS_pilot"].numbers["lid_wall"], 1.4)
        self.assertGreaterEqual(rows["V2_BOSS_pilot"].numbers["lid_od"], 5.0)
        island = [
            key[: -len("_pilot_d")]
            for key in rows["V2_BOSS_pilot"].numbers
            if key.endswith("_pilot_d") and key not in ("tail_pilot_d", "lid_pilot_d")
        ]
        self.assertEqual(len(island), 2, island)
        for name in island:
            self.assertAlmostEqual(
                rows["V2_BOSS_pilot"].numbers[f"{name}_pilot_d"], 2.10, delta=0.08
            )
            self.assertGreaterEqual(rows["V2_BOSS_pilot"].numbers[f"{name}_wall"], 1.4)
            self.assertGreaterEqual(rows["V2_BOSS_pilot"].numbers[f"{name}_od"], 5.0)
        self.assertTrue(rows["V2_EDGE_radii"].passed, rows["V2_EDGE_radii"].numbers)
        self.assertEqual(rows["V2_EDGE_radii"].numbers["flat_stations"], 0.0)
        self.assertGreaterEqual(rows["V2_EDGE_radii"].numbers["lid_rim_R"], 0.95)
        self.assertTrue(rows["V2_WALL_minima"].passed, rows["V2_WALL_minima"].numbers)
        self.assertFalse(rows["V2_USB_end"].passed)
        self.assertTrue(rows["V2_USB_end"].detail.startswith("NOT_APPLICABLE"), rows["V2_USB_end"].detail)
        self.assertIn("Q81: no receptacle at M1 52", rows["V2_USB_end"].detail)
        self.assertTrue(rows["V2_BOSS_sites"].passed, rows["V2_BOSS_sites"].numbers)
        self.assertLessEqual(rows["V2_BOSS_sites"].numbers["boss_1_err"], 0.05)
        self.assertLessEqual(rows["V2_BOSS_sites"].numbers["boss_2_err"], 0.05)
        self.assertEqual(rows["V2_BOSS_sites"].numbers["boss_1_courtyard_hits"], 0.0)
        self.assertEqual(rows["V2_BOSS_sites"].numbers["boss_2_courtyard_hits"], 0.0)
        self.assertAlmostEqual(rows["V2_BOSS_sites"].numbers["boss_1_table_u"], 13.23, places=2)
        self.assertAlmostEqual(rows["V2_BOSS_sites"].numbers["boss_2_table_u"], 17.95, places=2)
        self.assertGreaterEqual(rows["V2_BOSS_sites"].numbers["h1_h2_keep_gap"], 1.42 - 0.05)
        self.assertTrue(rows["V2_CHARGE_pads"].passed, rows["V2_CHARGE_pads"].numbers)
        self.assertEqual(rows["V2_CHARGE_pads"].numbers["P4_cap"], 0.0)
        self.assertEqual(rows["V2_CHARGE_pads"].numbers["P5_cap"], 0.0)
        self.assertEqual(rows["V2_CHARGE_pads"].numbers["P4_hole"], 1.0)
        self.assertEqual(rows["V2_CHARGE_pads"].numbers["P5_hole"], 1.0)
        self.assertEqual(rows["V2_CHARGE_pads"].numbers["P4_outer_open"], 1.0)
        self.assertEqual(rows["V2_CHARGE_pads"].numbers["P5_outer_open"], 1.0)
        self.assertNotIn("flush_pads", rows["V2_CHARGE_pads"].numbers)
        self.assertNotIn("P4_floor_t", rows["V2_CHARGE_pads"].numbers)
        self.assertGreaterEqual(rows["V2_CHARGE_pads"].numbers["nylon_between"], 3.0)
        self.assertAlmostEqual(rows["V2_CHARGE_pads"].numbers["P4_u"], 20.50, places=2)
        self.assertAlmostEqual(rows["V2_CHARGE_pads"].numbers["P4_s"], 4.35, places=2)
        self.assertAlmostEqual(rows["V2_CHARGE_pads"].numbers["P4_y"], 4.35, places=2)
        self.assertAlmostEqual(rows["V2_CHARGE_pads"].numbers["P5_u"], 20.50, places=2)
        self.assertAlmostEqual(rows["V2_CHARGE_pads"].numbers["P5_s"], 12.35, places=2)
        self.assertAlmostEqual(rows["V2_CHARGE_pads"].numbers["P5_y"], 4.35, places=2)
        self.assertGreaterEqual(rows["V2_CHARGE_pads"].numbers["P4_wall_around"], 1.45)
        self.assertGreaterEqual(rows["V2_CHARGE_pads"].numbers["P5_wall_around"], 1.45)
        self.assertGreaterEqual(rows["V2_CHARGE_pads"].numbers["P4_cell_gap"], 0.0)
        self.assertGreaterEqual(rows["V2_CHARGE_pads"].numbers["P5_cell_gap"], 0.0)
        self.assertGreaterEqual(rows["V2_CHARGE_pads"].numbers["P4_hinge_gap"], 0.0)
        self.assertGreaterEqual(rows["V2_CHARGE_pads"].numbers["P5_hinge_gap"], 0.0)
        self.assertTrue(rows["V2_CAVITY_v3"].passed, rows["V2_CAVITY_v3"].numbers)
        self.assertEqual(rows["V2_CAVITY_v3"].numbers["j2_inside"], 1.0)
        self.assertAlmostEqual(rows["V2_CAVITY_v3"].numbers["j2_u"], 15.15, places=2)
        self.assertAlmostEqual(rows["V2_CAVITY_v3"].numbers["j2_s"], 11.35, places=2)
        self.assertEqual(rows["V2_CAVITY_v3"].numbers["n_illegal"], 0.0)
        self.assertEqual(rows["V2_TAB_envelope"].numbers["side_pocket"], 0.0)
        self.assertEqual(rows["V2_TAB_envelope"].numbers["rib_slot_air"], 0.0)
        self.assertEqual(rows["V2_TAB_envelope"].numbers["drop_channel_air"], 0.0)
        self.assertAlmostEqual(rows["V2_TAB_envelope"].numbers["SIG1_strip"], 10.71, places=2)
        self.assertAlmostEqual(rows["V2_TAB_envelope"].numbers["SIG2_strip"], 21.81, places=2)
        self.assertEqual(rows["V2_WALL_minima"].numbers["P4_seat_open"], 1.0)
        self.assertEqual(rows["V2_WALL_minima"].numbers["P5_seat_open"], 1.0)
        self.assertGreaterEqual(rows["V2_WALL_minima"].numbers["P4_wall_around"], 1.45)
        self.assertGreaterEqual(rows["V2_WALL_minima"].numbers["P5_wall_around"], 1.45)
        self.assertAlmostEqual(self.params["BODY_WIDTH"], 22.0)
        self.assertAlmostEqual(self.params["BODY_THICK"], 9.0)
        self.assertAlmostEqual(self.params["CAVITY_U"][1], 20.5, places=2)
        self.assertAlmostEqual(self.params["BOARD_ZONE_U"][0], 2.25, places=2)
        self.assertAlmostEqual(self.params["BOARD_ZONE_U"][1], 19.75, places=2)
        self.assertAlmostEqual(self.params["BOARD_ZONE_S"][0], 16.00, places=2)
        self.assertAlmostEqual(self.params["RIB_S"][0], 14.9, places=2)
        stand = rows["V2_STANDOFF"].numbers
        for site in ("SIG1", "SIG2", "REF"):
            self.assertAlmostEqual(stand[f"{site}_well_af"], CAD.SHELL_HEX_AF, delta=0.01)
            self.assertLess(stand[f"{site}_well_af"] + CAD.PRINT_TOL, 2.0 * CAD.STANDOFF_AF / math.sqrt(3.0))
            self.assertAlmostEqual(rows["V2_RING_seat"].numbers[f"{site}_seat_d"], CAD.SHELL_RING_SEAT_D, delta=0.01)
            # Review r7: the dome is the bought titanium head; the print is open at the face.
            self.assertEqual(rows["V2_RING_seat"].numbers[f"{site}_face_open"], 1.0, site)
        for name in ("CLOSURE_PASSED", "KEEPOUT_SIGNAL_air", "KEEPOUT_REF_air", "CABLE_EXIT_cavity"):
            self.assertFalse(rows[name].passed, name)
            self.assertTrue(rows[name].detail.startswith("NOT_MEASURED"), name)
        self.assertEqual(sum(1 for c in checks if c.name == "V2_STANDOFF"), 1)
        self.assertEqual(self.notes["stage_b_cuts"]["exit_removed_mm3"], 0.0)
        wall = rows["V2_WALL_minima"].numbers
        self.assertGreaterEqual(wall["slot_wall_s_left"], 1.0)
        self.assertGreaterEqual(wall["slot_wall_s_right"], 1.0)
        self.assertGreaterEqual(wall["slot_floor_y"], 1.0)
        self.assertGreaterEqual(wall["slot_clear_u"], 0.15)
        self.assertIn("q59", self.notes)
        self.assertIn("REF_end_wall_slot", self.notes["q59"])
        self.assertIn("packing-v2.md", self.notes["q59"])

    def test_two_consecutive_shell_runs_are_identical(self) -> None:
        cmd = [
            sys.executable,
            str(SCRIPT),
            "--params",
            str(SHELL_FILE),
            "--stage",
            "shell",
        ]
        hashes = []
        for _ in range(2):
            with tempfile.TemporaryDirectory() as temp_dir:
                dest = Path(temp_dir)
                done = subprocess.run(
                    cmd + ["--out", str(dest)], capture_output=True, text=True
                )
                self.assertEqual(
                    done.returncode, 0, done.stderr + done.stdout
                )
                payload = json.loads((dest / "manifest.json").read_text(encoding="utf-8"))
                hashes.append(payload["files"])
                self.assertEqual(payload["stage_b_failing"], [])
                for part in ("body_full_p15.step", "lid.step", "body_full_p15.stl", "lid.stl"):
                    self.assertEqual(
                        (dest / part).read_bytes(), (CAD.V2_DIR / part).read_bytes(), part
                    )
                self.assertEqual(payload["stage"], "shell")
                self.assertEqual(payload["winner"], CAD.SHELL_WINNER)
                self.assertTrue(payload["provisional"])
                load_manifest_mod().validate(payload)
        self.assertEqual(hashes[0], hashes[1])
        committed = json.loads((CAD.V2_DIR / "manifest.json").read_text(encoding="utf-8"))
        self.assertEqual(hashes[0], committed["files"])


@unittest.skipUnless(HAS_RENDER, "needs the cad extra: matplotlib and trimesh")
class CadShellV2StampTests(unittest.TestCase):
    def test_stamp_text_equals_manifest_commit(self) -> None:
        render = load_render_mod()
        payload = json.loads((CAD.V2_DIR / "manifest.json").read_text(encoding="utf-8"))
        commit = payload["commit"]
        self.assertRegex(commit, r"^[0-9a-f]{40}$")
        date = render.git_commit_date(commit)
        self.assertEqual(
            render.stamp_label(commit, date),
            f"solids commit {commit[:12]}  {date}",
        )
        dirty = "0123456789abcdef0123456789abcdef01234567 dirty"
        self.assertEqual(
            render.stamp_label(dirty, "2026-09-18"),
            "solids commit 0123456789ab dirty  2026-09-18",
        )
        self.assertEqual(render.solids_stamp_commit(payload, CAD.V2_DIR), commit)

    def test_manifest_commit_is_the_last_change_to_the_solids(self) -> None:
        payload = json.loads((CAD.V2_DIR / "manifest.json").read_text(encoding="utf-8"))
        self.assertEqual(payload["commit"], CAD.git_commit_solids(ROOT, CAD.V2_DIR))


class CadShellV4ManifestTests(unittest.TestCase):
    def test_clearance_gate_rejects_a_near_miss_and_overlap(self) -> None:
        spec = importlib.util.spec_from_file_location(
            "build_shell_v4", ROOT / "scripts/cad/build_shell_v4.py")
        module = importlib.util.module_from_spec(spec)
        assert spec.loader is not None
        spec.loader.exec_module(module)
        self.assertFalse(module.courtyard_passes(0, 0, 0.3999, False))
        self.assertTrue(module.courtyard_passes(0, 0, 0.40, False))
        self.assertFalse(module.courtyard_passes(.01, 0, .50, False))
        self.assertFalse(module.courtyard_passes(0, .01, 0, True))

    def test_manifests_cover_current_board_courtyards(self) -> None:
        table = (ROOT / "docs/fab/board-v4-design.md").read_text(encoding="utf-8")
        table = table.split("#### Courtyards on the island")[1].split("#### Rings, strip roots")[0]
        refs = {
            fields[0]
            for line in table.splitlines()
            if len(fields := [f.strip() for f in line.strip().strip("|").split("|")]) == 12
            and fields[1] in ("top", "bottom")
        }
        for variant in ("v4", "v4-m16", "v4-snap"):
            with self.subTest(variant=variant):
                payload = json.loads((ROOT / f"docs/fab/cad/{variant}/manifest.json").read_text())
                self.assertEqual(payload["source_table_sha256"], hashlib.sha256(table.encode()).hexdigest())
                rows = {c["item"]: c for c in payload["checks"] if c["item"] in refs}
                self.assertEqual(set(rows), refs)
                self.assertEqual(rows["C3"]["kind"], "top courtyard")
                self.assertEqual(rows["C18"]["kind"], "bottom courtyard")
                self.assertEqual(rows["C19"]["kind"], "top courtyard")
                self.assertTrue(all(row["passed"] for row in rows.values()))
                for ref, row in rows.items():
                    with self.subTest(variant=variant, ref=ref):
                        if ref == "U1":
                            self.assertEqual(row["intended_seat"], "P2 lid post on U1 top")
                            self.assertEqual(row["margin_mm"], 0)
                            self.assertEqual(row["lid_overlap_mm3"], 0)
                        elif row["margin_mm"] is not None:
                            self.assertIsNone(row["intended_seat"])
                            self.assertGreaterEqual(row["margin_mm"], 0.40)

    def test_folded_wall_flap_is_checked_and_clear(self) -> None:
        # The original plate check stopped at s14.85. The lower flap past
        # the rib hit 1.184 mm³ of the r9 bay shoulder despite 97 passes.
        payload = json.loads((ROOT / "docs/fab/cad/v4/manifest.json").read_text())
        rows = [c for c in payload["checks"] if c["item"] == "P4/P5 folded flap"]
        self.assertEqual(len(rows), 1)
        self.assertTrue(rows[0]["passed"])
        self.assertEqual(rows[0]["overlap_mm3"], 0.0)
        self.assertGreater(payload["notes"]["shell_measure"]["flap_relief_removed_mm3"], 0)

    def test_snap_key_volume_and_opposing_print_offsets(self) -> None:
        payload = json.loads((ROOT / "docs/fab/cad/v4-snap/manifest.json").read_text())
        checks = payload["checks"]
        self.assertEqual(len(checks), 106)
        self.assertTrue(all(c["passed"] for c in checks))
        flap = next(c for c in checks if c["item"] == "P4/P5 folded flap")
        self.assertEqual(flap["overlap_mm3"], 0)
        keys = [c for c in checks if c["item"].startswith("key ")]
        self.assertEqual(len(keys), 3)
        for key in keys:
            with self.subTest(key=key["item"]):
                self.assertEqual(key["body_overlap_mm3"], 0)
                self.assertLessEqual(key["lid_overlap_mm3"], .001)
        self.assertGreater(keys[-1]["intended_foot_contact_mm3"], 0)
        offsets = [c for c in checks if c["kind"] == "rebuilt opposing tolerance stack"]
        self.assertEqual(len(offsets), 2)
        for row in offsets:
            with self.subTest(offset=row["ledge_offset_mm"]):
                self.assertGreater(row["engagement_mm"], 0)
                self.assertLess(row["closing_overlap_mm3"], .001)
                self.assertGreater(row["vertical_ledge_gap_worst_mm"], 0)
                self.assertGreater(row["vertical_floor_gap_worst_mm"], 0)


class CadShellV2PackingSourceTests(unittest.TestCase):
    def test_pinned_packing_matches_this_repo(self) -> None:
        """Review r7: the shell reads §5d from this repo at a pinned sha, never another worktree."""
        text, sha, label = CAD._s5c_packing_text()
        self.assertEqual(label, "docs/fab/packing-v2.md")
        self.assertEqual(sha, CAD.S5D_PACKING_SHA)
        live = (ROOT / "docs" / "fab" / "packing-v2.md").read_text(encoding="utf-8")
        self.assertEqual(CAD._parse_s5d_folded_pads(text), CAD._parse_s5d_folded_pads(live))
        self.assertEqual(CAD._parse_s5d_shell_extras(text), CAD._parse_s5d_shell_extras(live))
        s5e_text, s5e_sha, s5e_label = CAD._s5e_packing_text()
        self.assertEqual(s5e_label, "docs/fab/packing-v2.md")
        self.assertEqual(s5e_sha, CAD.S5E_PACKING_SHA)
        pads = CAD._parse_s5e_shell_pads(s5e_text)
        self.assertEqual(pads["P4"][0], 20.50)
        self.assertEqual(pads["P5"][0], 20.50)
        self.assertEqual(pads["P4"][4], "+u")
        payload = json.loads((CAD.V2_DIR / "manifest.json").read_text(encoding="utf-8"))
        self.assertNotIn(".worktrees", json.dumps(payload))


if __name__ == "__main__":
    unittest.main()
