uguryildirim24/elicio/tests/test_receiver_v2.py

from __future__ import annotations

import io
import json
import tempfile
import unittest
from contextlib import redirect_stdout
from pathlib import Path

from elicio.cli import main
from elicio.pipeline.load import Recording
from elicio.frame_v2 import FRAME_V2_MAX_SAMPLES, Flag, MsgType, fragment, pack_stream
from elicio.receiver_v2 import (
    DROPOUT_INTERVALS,
    EXIT_DROPOUT_3_4,
    EXIT_NOT_A_SESSION,
    EXIT_SAME_CRITERION_FAILED,
    FRAME_CASES,
    LOADER_NAME,
    RAIL_CODE,
    SAME_CRITERION,
    _meta,
    _sample_bytes,
    pack_ads_sample,
    assert_pin_map_matches,
    case_packets,
    check_session,
    dump_fixture_packets,
    live_fake_packets,
    load_fixture_packets,
    load_receiver_session,
    receive_packets,
)

ROOT = Path(__file__).resolve().parents[1]
FIXTURES = ROOT / "tests" / "fixtures" / "receiver_v2"
BOARD_MD = ROOT / "docs" / "fab" / "board-v2.md"
MONTAGE_MD = ROOT / "docs" / "fab" / "montage.md"
PINS_H = ROOT / "firmware" / "src" / "board_pins_v2.h"


def _flat_packets(acq: int, count: int, seq: int) -> list[bytes]:
    """``count`` equal samples from ``acq`` on (rail code on both channels)."""
    sample = pack_ads_sample(0xC00000, RAIL_CODE, RAIL_CODE)
    packets: list[bytes] = []
    while count:
        n = min(FRAME_V2_MAX_SAMPLES, count)
        packets += fragment(MsgType.STREAM, 7, seq, pack_stream(_meta(n, acq, seq), sample * n), 244)
        acq += n
        seq += 1
        count -= n
    return packets


def _run(argv: list[str]) -> tuple[int, str]:
    buf = io.StringIO()
    with redirect_stdout(buf):
        code = main(argv)
    return code, buf.getvalue()


class ReceiverV2Tests(unittest.TestCase):
    def test_committed_fixtures_equal_the_generators(self) -> None:
        # Review r6: the tests read the committed fixtures; they no longer
        # rewrite them on every run. Regenerate with dump_fixture_packets.
        cases = {name: case_packets(name) for name in FRAME_CASES + ("dropout", "undervoltage", "vbus")}
        cases["simulate_live"] = live_fake_packets()
        for name, packets in cases.items():
            with self.subTest(name=name):
                self.assertEqual(load_fixture_packets(FIXTURES / f"{name}.json"), packets)

    def test_pin_header_matches_board_v2_section_9(self) -> None:
        assert_pin_map_matches(BOARD_MD.read_text(encoding="utf-8"), PINS_H.read_text(encoding="utf-8"))

    def test_pipeline_loader_round_trip(self) -> None:
        with tempfile.TemporaryDirectory() as tmp:
            out = Path(tmp) / "sess"
            receive_packets(case_packets("normal"), out, "bench", "s2")
            recording = load_receiver_session(out)
            self.assertIsInstance(recording, Recording)
            self.assertEqual(recording.signal.dtype, "float32")
            self.assertEqual(recording.labels.dtype, "int32")
            self.assertEqual(recording.signal.shape, (4, 2))
            self.assertEqual(recording.channel_names, ["ADS_CH1", "ADS_CH2"])
            self.assertEqual(recording.sample_rate, 2000.0)
            codes = recording.extra["codes_int32"]
            self.assertEqual(codes.dtype, "int32")
            self.assertTrue((recording.signal == codes.astype("float32")).all())
            meta = json.loads((out / "meta.json").read_text(encoding="utf-8"))
            self.assertEqual(meta["loader"], LOADER_NAME)

    def test_every_frame_v2_case_through_the_receiver(self) -> None:
        expected = {
            "normal": {"samples": 4},
            "wrap": {"samples": 4, "wraps": 1},
            "fragment": {"samples": 3},
            "reorder": {"samples": 3},
            "loss": {"samples": 2, "losses": 1},
            "overrun": {"samples": 1, "overruns": 1},
            "partial": {"samples": 0},
            "reconnect": {"samples": 0, "reconnects": 1},
            "bad_crc": {"errors": "bad_crc"},
            "version_mismatch": {"errors": "version_mismatch"},
        }
        for name, want in expected.items():
            with self.subTest(name=name):
                packets = load_fixture_packets(FIXTURES / f"{name}.json")
                with tempfile.TemporaryDirectory() as tmp:
                    out = Path(tmp) / name
                    receive_packets(packets, out, "bench", name)
                    sidecar = json.loads((out / "sidecar.json").read_text(encoding="utf-8"))
                    recording = load_receiver_session(out)
                    if "samples" in want:
                        self.assertEqual(recording.signal.shape[0], want["samples"])
                    if "wraps" in want:
                        self.assertGreaterEqual(sidecar["wrap_count"], want["wraps"])
                    if "losses" in want:
                        self.assertGreaterEqual(sidecar["transport_loss_count"], want["losses"])
                    if "overruns" in want:
                        self.assertGreaterEqual(sidecar["overrun_count"], want["overruns"])
                    if "reconnects" in want:
                        self.assertGreaterEqual(sidecar["reconnect_count"], want["reconnects"])
                    if "errors" in want:
                        self.assertIn(want["errors"], sidecar["decode_errors"])

    def test_undervoltage_and_vbus_are_events(self) -> None:
        for name, kind in (("undervoltage", "undervoltage"), ("vbus", "vbus")):
            with self.subTest(name=name):
                with tempfile.TemporaryDirectory() as tmp:
                    out = Path(tmp) / name
                    receive_packets(case_packets(name), out, "bench", name)
                    sidecar = json.loads((out / "sidecar.json").read_text(encoding="utf-8"))
                    kinds = [event["kind"] for event in sidecar["events"]]
                    self.assertIn(kind, kinds)

    def test_simulate_live_injects_faults(self) -> None:
        with tempfile.TemporaryDirectory() as tmp:
            out = Path(tmp) / "live"
            receive_packets(live_fake_packets(), out, "bench", "live")
            sidecar = json.loads((out / "sidecar.json").read_text(encoding="utf-8"))
            self.assertGreaterEqual(sidecar["transport_loss_count"], 1)
            self.assertGreaterEqual(sidecar["reconnect_count"], 1)
            self.assertGreaterEqual(sidecar["overrun_count"], 1)
            self.assertGreater(load_receiver_session(out).signal.shape[0], 0)
            self.assertTrue(sidecar["batteries"])

    def test_cli_simulate_and_check_pass(self) -> None:
        with tempfile.TemporaryDirectory() as tmp:
            out = Path(tmp) / "cli"
            code, text = _run(
                ["receive", "--simulate", str(FIXTURES / "normal.json"), "--out", str(out)]
            )
            self.assertEqual(code, 0)
            self.assertIn("simulate", text)
            code, text = _run(["receive-check", str(out)])
            self.assertEqual(code, 0)
            summary = json.loads(text)
            self.assertEqual(summary["sample_count"], 4)
            self.assertTrue(summary["ok"])
            self.assertNotIn("S2 continues (Q75)", text)

    def test_cli_simulate_live(self) -> None:
        with tempfile.TemporaryDirectory() as tmp:
            out = Path(tmp) / "live"
            code, _text = _run(["receive", "--simulate-live", "--out", str(out)])
            self.assertEqual(code, 0)
            code, text = _run(["receive-check", str(out)])
            self.assertEqual(code, 0)
            summary = json.loads(text)
            self.assertGreater(summary["sample_count"], 0)
            self.assertGreaterEqual(summary["losses"], 1)

    def test_receive_check_dropout_only_is_exit_3_and_s2_continues(self) -> None:
        with tempfile.TemporaryDirectory() as tmp:
            out = Path(tmp) / "drop"
            receive_packets(case_packets("dropout"), out, "bench", "drop")
            summary = check_session(out)
            self.assertGreater(summary["dropout_count"], 0)
            self.assertEqual(summary["same_criterion_failed"], [])
            self.assertEqual(summary["exit_code"], EXIT_DROPOUT_3_4)
            code, text = _run(["receive-check", str(out)])
            self.assertEqual(code, EXIT_DROPOUT_3_4)
            self.assertIn("S2 continues (Q75); dropout count goes in the session note", text)
            self.assertIn(f"dropout count: {summary['dropout_count']}", text)
            self.assertIn("longest run:", text)
            self.assertIn("sample intervals", text)
            self.assertIn("beginning at acq_index", text)
            sidecar = json.loads((out / "sidecar.json").read_text(encoding="utf-8"))
            self.assertEqual(sidecar["dropout_count"], summary["dropout_count"])

    def test_receive_check_same_criterion_with_dropout_is_exit_1(self) -> None:
        with tempfile.TemporaryDirectory() as tmp:
            out = Path(tmp) / "both"
            receive_packets(case_packets("dropout"), out, "bench", "both")
            sidecar_path = out / "sidecar.json"
            sidecar = json.loads(sidecar_path.read_text(encoding="utf-8"))
            sidecar["same_criterion"]["3.7"] = "fail"
            sidecar_path.write_text(json.dumps(sidecar) + "\n", encoding="utf-8")
            code, text = _run(["receive-check", str(out)])
            self.assertEqual(code, EXIT_SAME_CRITERION_FAILED)
            self.assertIn("dropout count:", text)
            self.assertNotIn("S2 continues (Q75)", text)

    def test_dropout_threshold_is_more_than_200_intervals(self) -> None:
        for count, stretches in ((DROPOUT_INTERVALS + 1, 0), (DROPOUT_INTERVALS + 2, 2)):  # both channels
            with self.subTest(samples=count):
                with tempfile.TemporaryDirectory() as tmp:
                    out = Path(tmp) / "edge"
                    receive_packets(_flat_packets(0, count, 1), out, "bench", "edge")
                    self.assertEqual(check_session(out)["dropout_stretches"], stretches)

    def test_restart_window_does_not_hide_earlier_dropout(self) -> None:
        # A flat run at acq 0..204, then a RESTART at acq 1000: only
        # 1000..1199 are excluded; the early dropout still counts.
        packets = _flat_packets(0, DROPOUT_INTERVALS + 5, 1)
        seq = 1 + len(packets)
        logical = pack_stream(_meta(4, 1000, seq, Flag.RESTART), _sample_bytes(4, 9))
        packets += fragment(MsgType.STREAM, 7, seq, logical, 244)
        with tempfile.TemporaryDirectory() as tmp:
            out = Path(tmp) / "restart"
            receive_packets(packets, out, "bench", "restart")
            summary = check_session(out)
            self.assertEqual(summary["dropout_stretches"], 2)  # both channels
            self.assertEqual(summary["exit_code"], EXIT_DROPOUT_3_4)

    def test_receive_check_on_a_missing_session_exits_2(self) -> None:
        with tempfile.TemporaryDirectory() as tmp:
            self.assertEqual(_run(["receive-check", str(Path(tmp) / "nothing")])[0], EXIT_NOT_A_SESSION)

    def test_receive_check_fails_scored_same_criterion(self) -> None:
        with tempfile.TemporaryDirectory() as tmp:
            out = Path(tmp) / "same"
            receive_packets(case_packets("normal"), out, "bench", "same")
            sidecar_path = out / "sidecar.json"
            sidecar = json.loads(sidecar_path.read_text(encoding="utf-8"))
            sidecar["same_criterion"]["3.7"] = "fail"
            sidecar_path.write_text(json.dumps(sidecar) + "\n", encoding="utf-8")
            self.assertEqual(_run(["receive-check", str(out)])[0], EXIT_SAME_CRITERION_FAILED)

    def test_every_montage_section_8_line(self) -> None:
        """Review r7: walk montage §8. "same criterion" lines stop (exit 1) when
        scored fail; the revised lines 3.1–3.4 are not scored by this tool."""
        text = MONTAGE_MD.read_text(encoding="utf-8")
        section = text[text.index("## 8. Protocol v2 mapping"):]
        end = section.find("\n## ", 1)
        section = section if end < 0 else section[:end]
        same, revised = [], []
        for line in section.splitlines():
            cells = [c.strip() for c in line.strip().strip("|").split("|")]
            if len(cells) == 3 and cells[0].startswith("3."):
                (same if cells[2].startswith("same criterion") else revised).append(cells[0])
        self.assertEqual(tuple(same), SAME_CRITERION)
        self.assertEqual(revised, ["3.1", "3.2", "3.3", "3.4"])
        with tempfile.TemporaryDirectory() as tmp:
            out = Path(tmp) / "walk"
            receive_packets(case_packets("normal"), out, "bench", "walk")
            sidecar_path = out / "sidecar.json"
            base = json.loads(sidecar_path.read_text(encoding="utf-8"))
            self.assertEqual(check_session(out)["exit_code"], 0)
            for key, value, expected in (
                *((k, "fail", EXIT_SAME_CRITERION_FAILED) for k in same),
                *((k, "pass", 0) for k in same),
                *((k, "not_scored", 0) for k in same),
                *((k, "fail", 0) for k in revised),
            ):
                with self.subTest(line=key, value=value):
                    sidecar = json.loads(json.dumps(base))
                    sidecar["same_criterion"][key] = value
                    sidecar_path.write_text(json.dumps(sidecar) + "\n", encoding="utf-8")
                    summary = check_session(out)
                    self.assertEqual(summary["exit_code"], expected)
                    self.assertEqual(_run(["receive-check", str(out)])[0], expected)

    def test_bleak_is_optional_for_the_fake_path(self) -> None:
        import elicio.receiver_v2 as mod

        self.assertTrue(hasattr(mod, "PacketSource"))
        self.assertNotIn("bleak", dir(mod))


if __name__ == "__main__":
    unittest.main()
